radioelf/DPS5015--Nextion/test_py/dps5015_limits.ini

[SectionZero]
The parameters below limit the code from incorrectly transmitting extreme values entered by the user:
if threshold exceeded value defaults to zero:
This file may be adapted for other versions of 'DPSxxxx' power supplies:

[SectionOne]
voltage_set_max: 50.0
voltage_set_min: 0.0
current_set_max: 15.0
current_set_min: 0.0
lock_set_max: 1
lock_set_min: 0
onoff_set_max: 1
onoff_set_min: 0
b_led_set_max: 15
b_led_set_min: 0
extract_m_set_max: 1
extract_m_set_min: 0

voltage_set2_max: 50.0
voltage_set2_min: 0.0
current_set2_max: 15.0
current_set2_min: 0.0
s_ovp_set_max: 51.0
s_ovp_set_min: 0.0
s_ocp_set_max: 15.1
s_ocp_set_min: 0.0
s_opp_set_max: 751.0
s_opp_set_min: 0.0
b_led2_set_max: 15
b_led2_set_min: 0
m_pre_set_max: 9
m_pre_set_min: 0
s_ini_set_max: 1
s_ini_set_min: 0

[Others]
Route: not implemented
